muzy/RoboticsResearch/paper/images/mounting.pdf

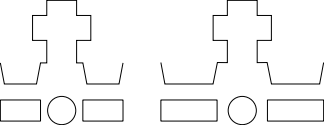
[picture p39: figure]
