muzy/RoboticsResearch/hardware/edubot_board_v01.png

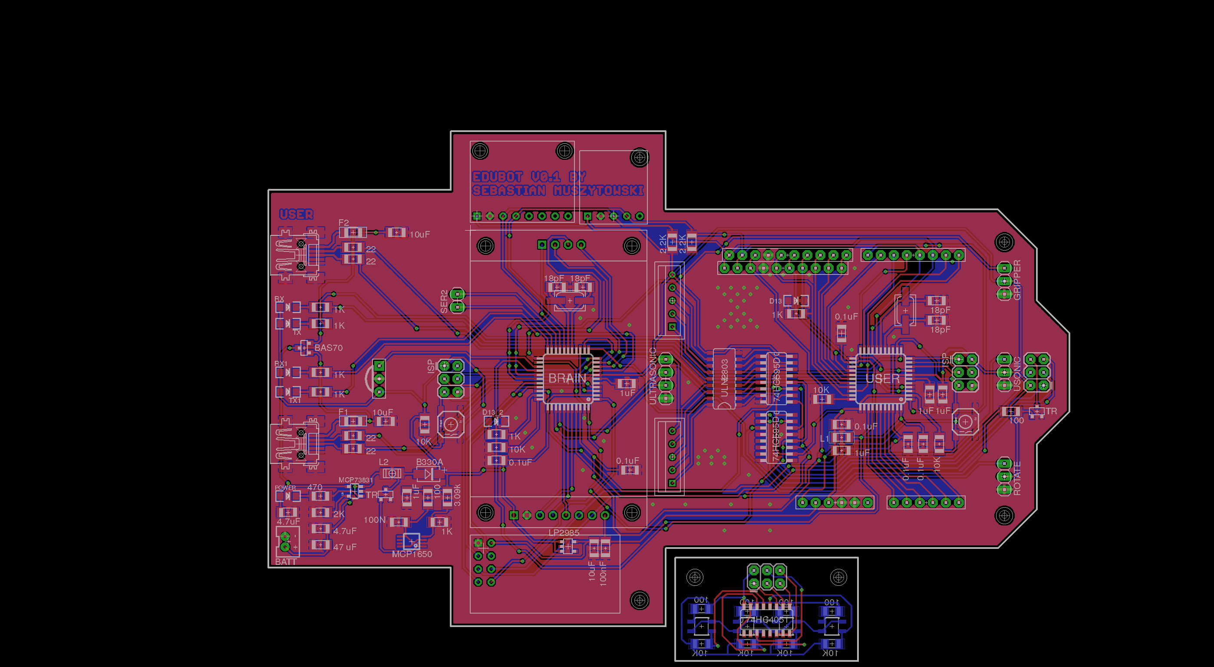
hardware/edubot_board_v01.png
