muzy/RoboticsResearch/hardware/edubot_board_v011.png

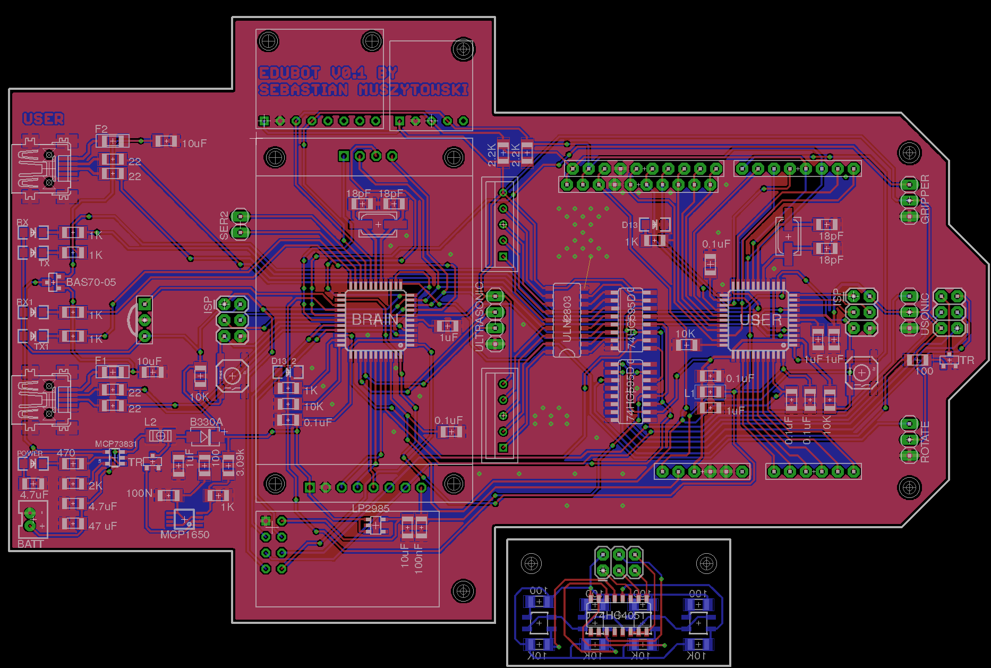
hardware/edubot_board_v011.png
