muzy/RoboticsResearch/hardware/edubot_board_v012.png

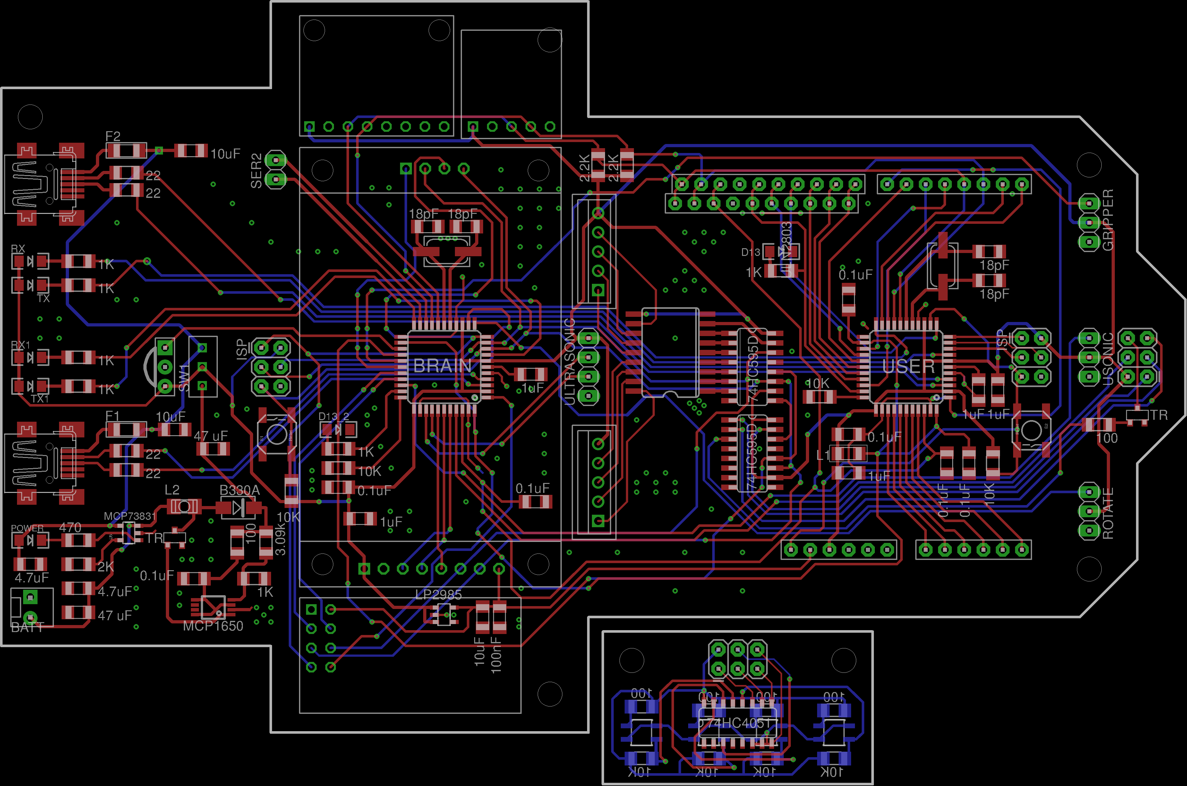
hardware/edubot_board_v012.png
