muzy/RoboticsResearch/hardware/edubot_schematic_v01.png

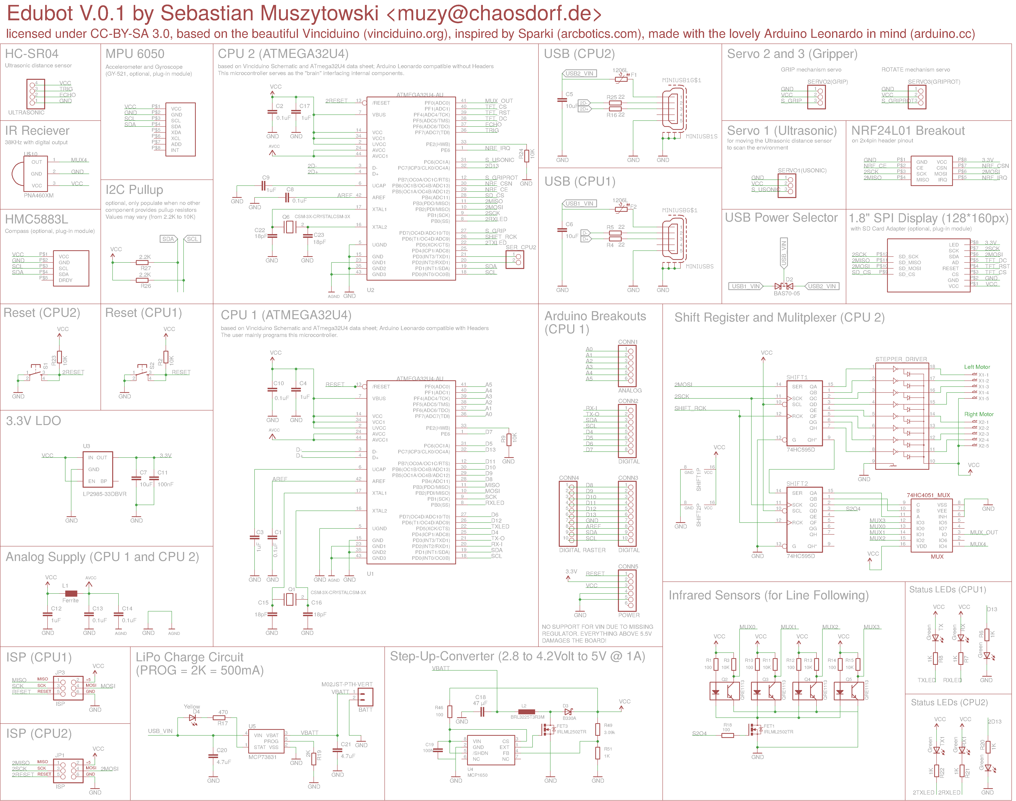
hardware/edubot_schematic_v01.png
