muzy/RoboticsResearch/hardware/edubot_schematic_v012.png

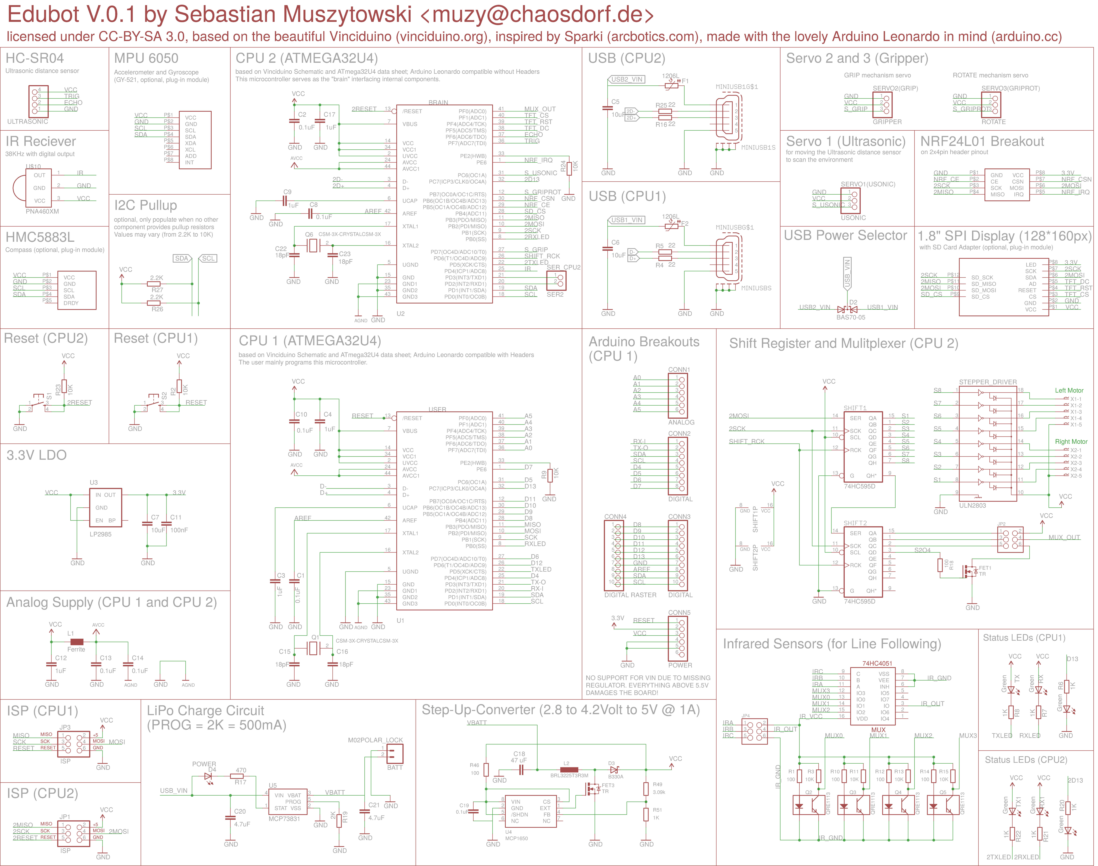
hardware/edubot_schematic_v012.png
