muzy/RoboticsResearch/hardware/schematic_backup_save.png

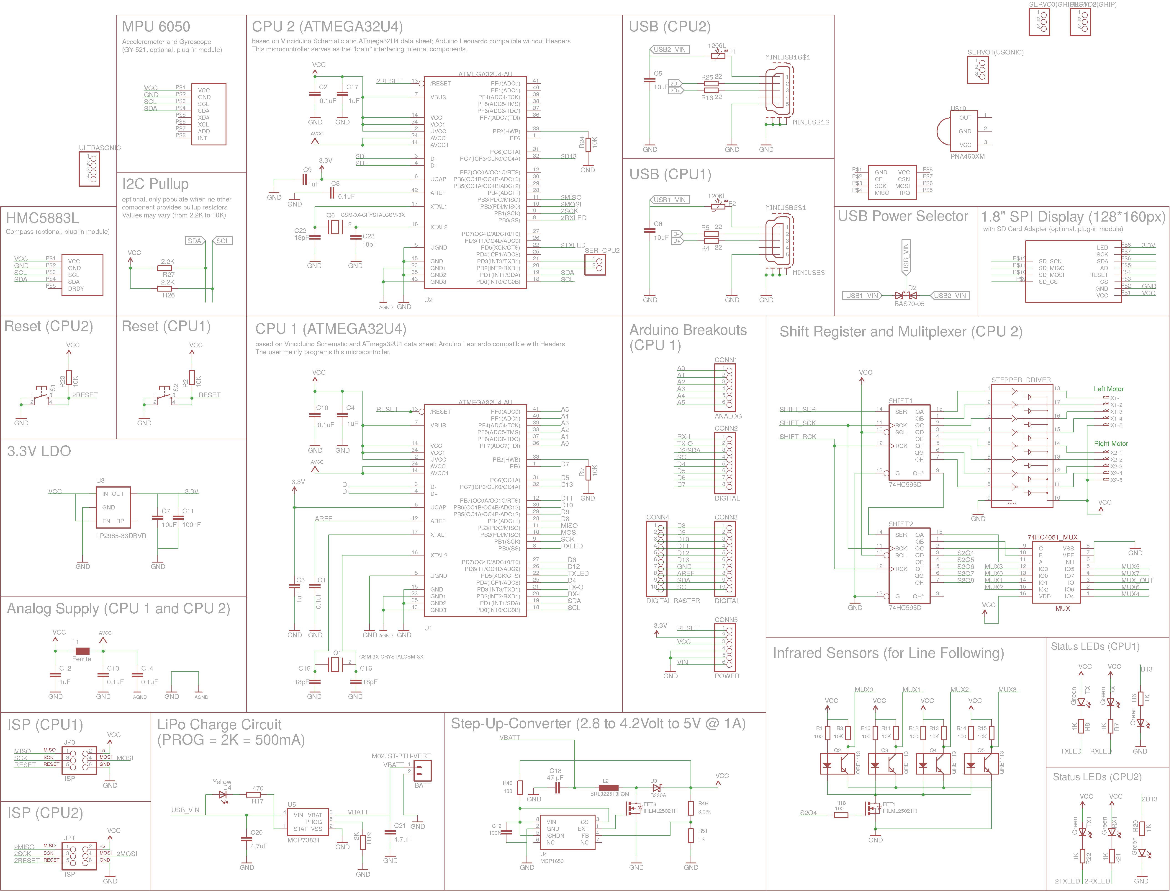
hardware/schematic_backup_save.png
