muzy/RoboticsResearch/paper/images/30_wheel_side.jpg

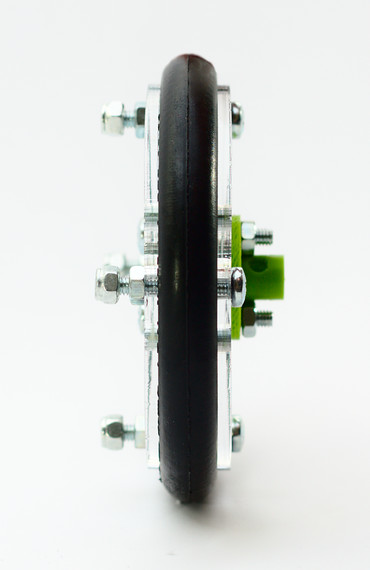
paper/images/30_wheel_side.jpg
