muzy/RoboticsResearch/paper/images/schematic/cpu1.png

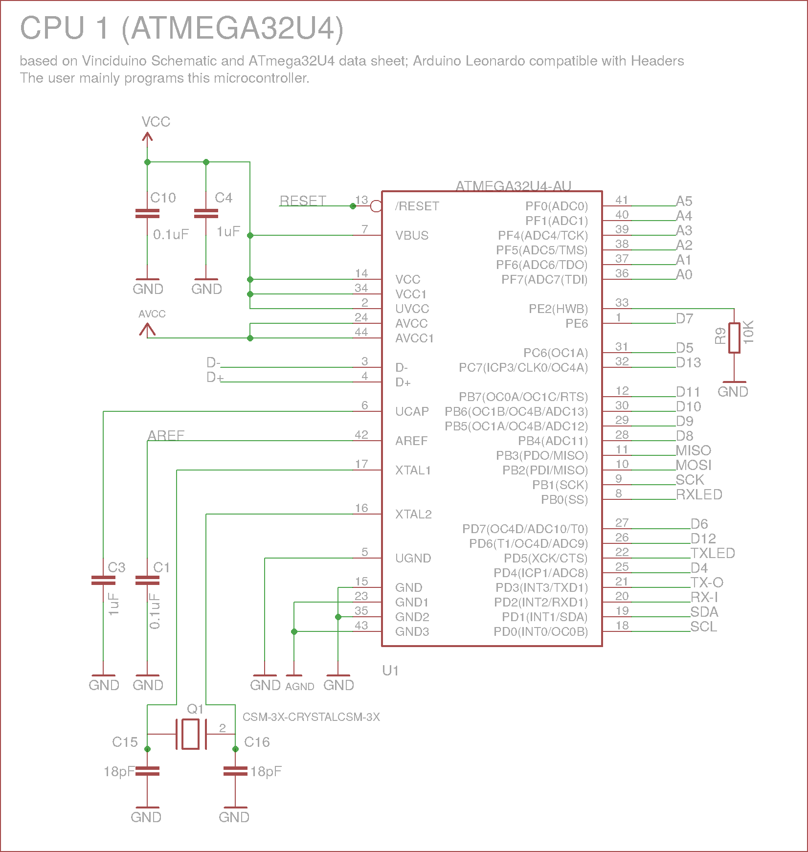
paper/images/schematic/cpu1.png
