muzy/RoboticsResearch/paper/images/schematic/cpu2.png

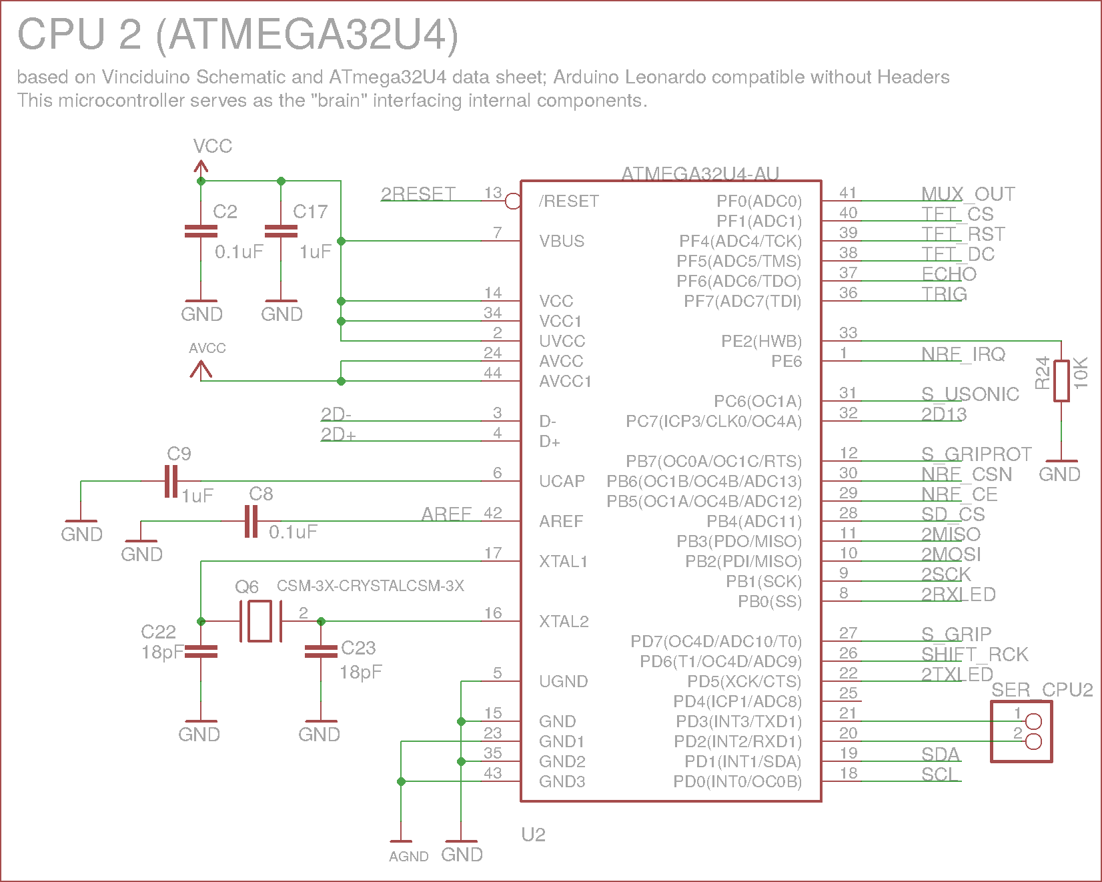
paper/images/schematic/cpu2.png
