muzy/RoboticsResearch/paper/images/schematic/reset.png

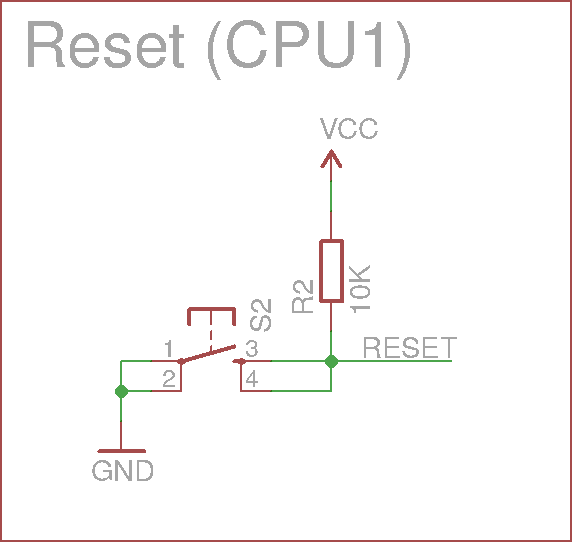
paper/images/schematic/reset.png
