muzy/RoboticsResearch/paper/images/schematic/robot_schematic_optional.png

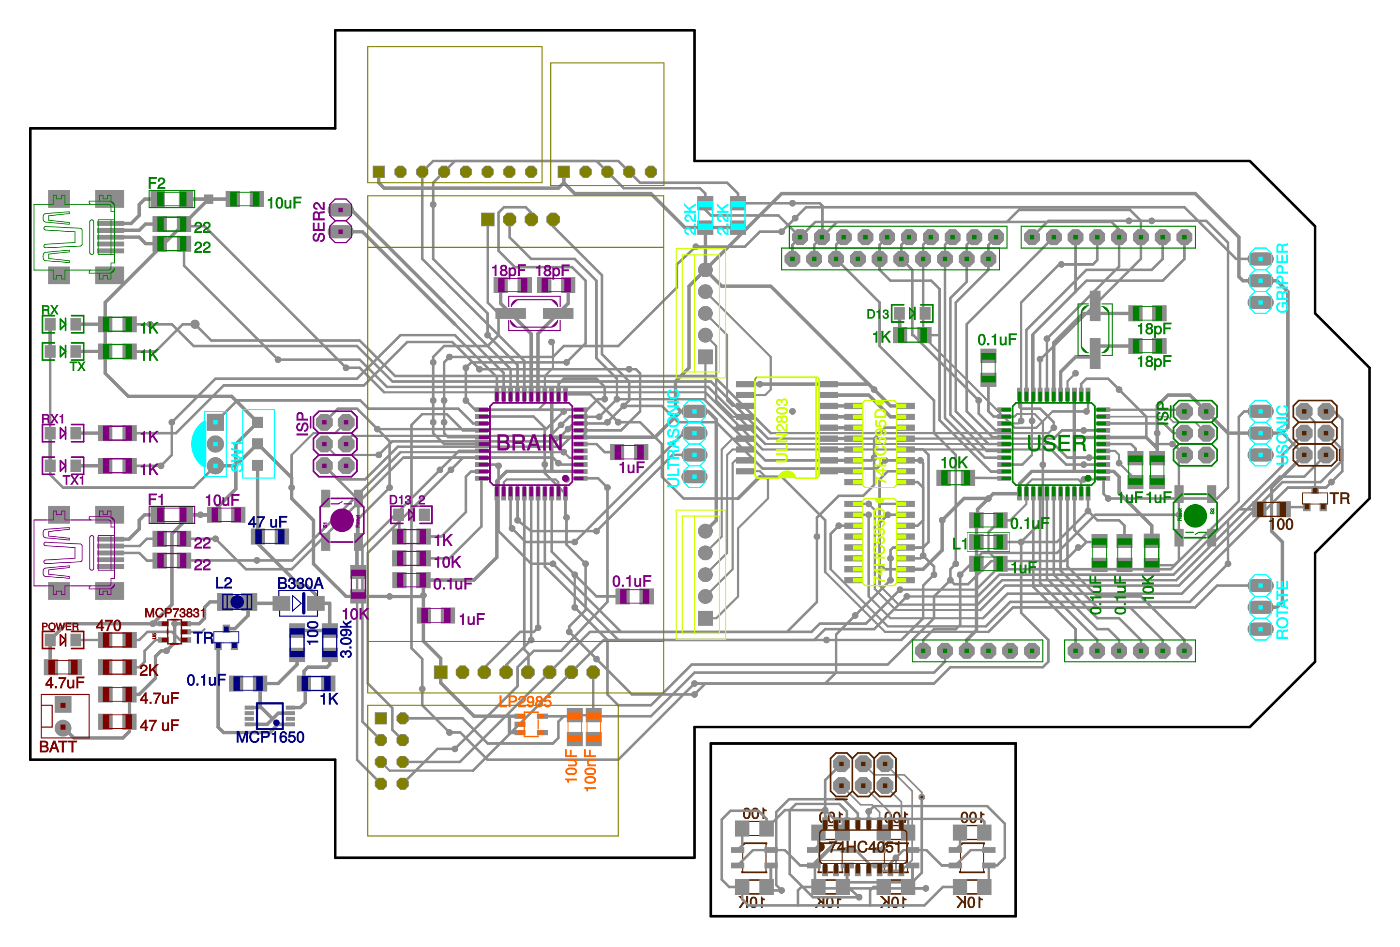
paper/images/schematic/robot_schematic_optional.png
