muzy/RoboticsResearch/paper/images/schematic/shift.png

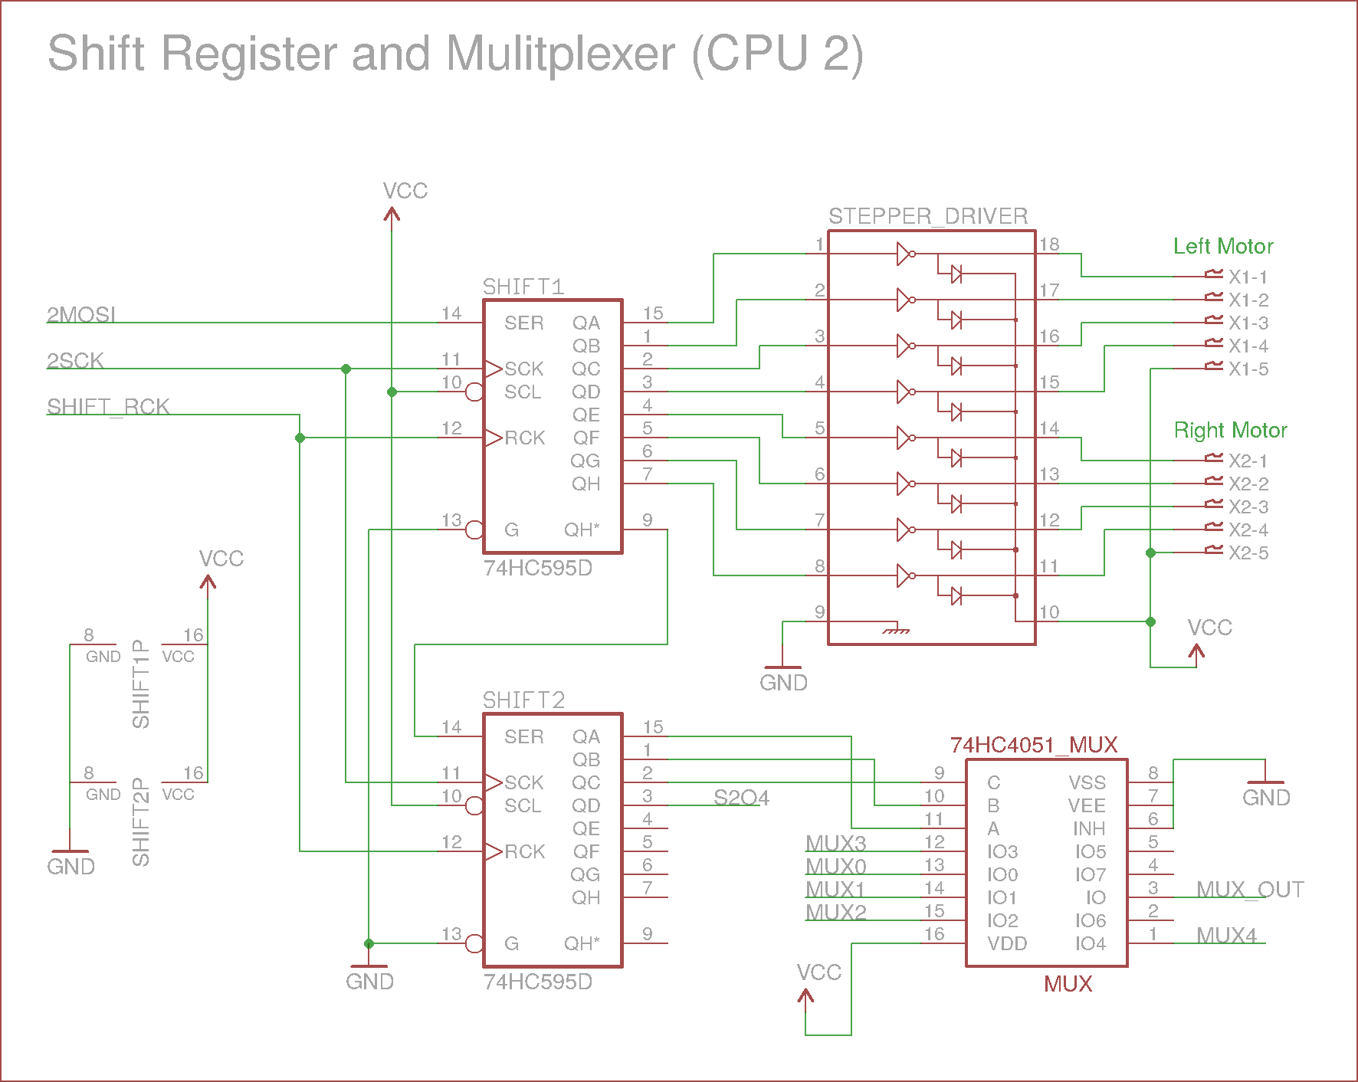
paper/images/schematic/shift.png
