muzy/RoboticsResearch/paper/images/schematic/robot_schematic.pdf

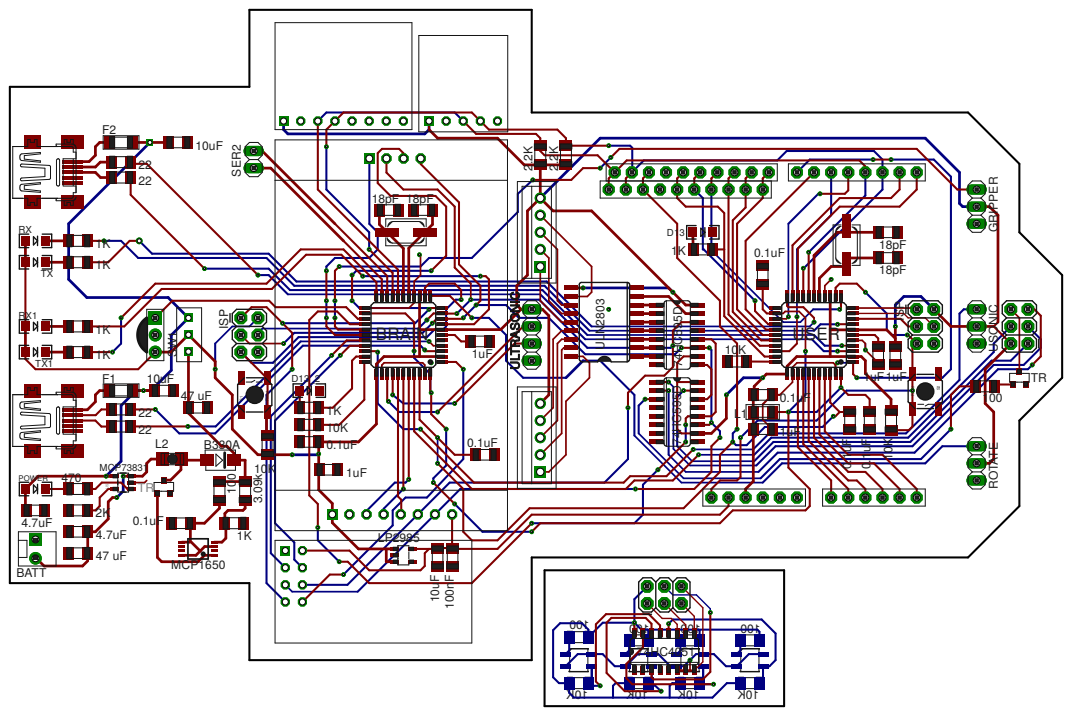
[picture p60: page 1]
BATT; NIC; Reset; ISP; USER; ULN2803; MCP1650; POWER; MCP73831; 10KReset; BRAIN; SER2

USONIC GRIPPER ROTATE
