muzy/RoboticsResearch/paper/images/schematic/robot_schematic_user.pdf

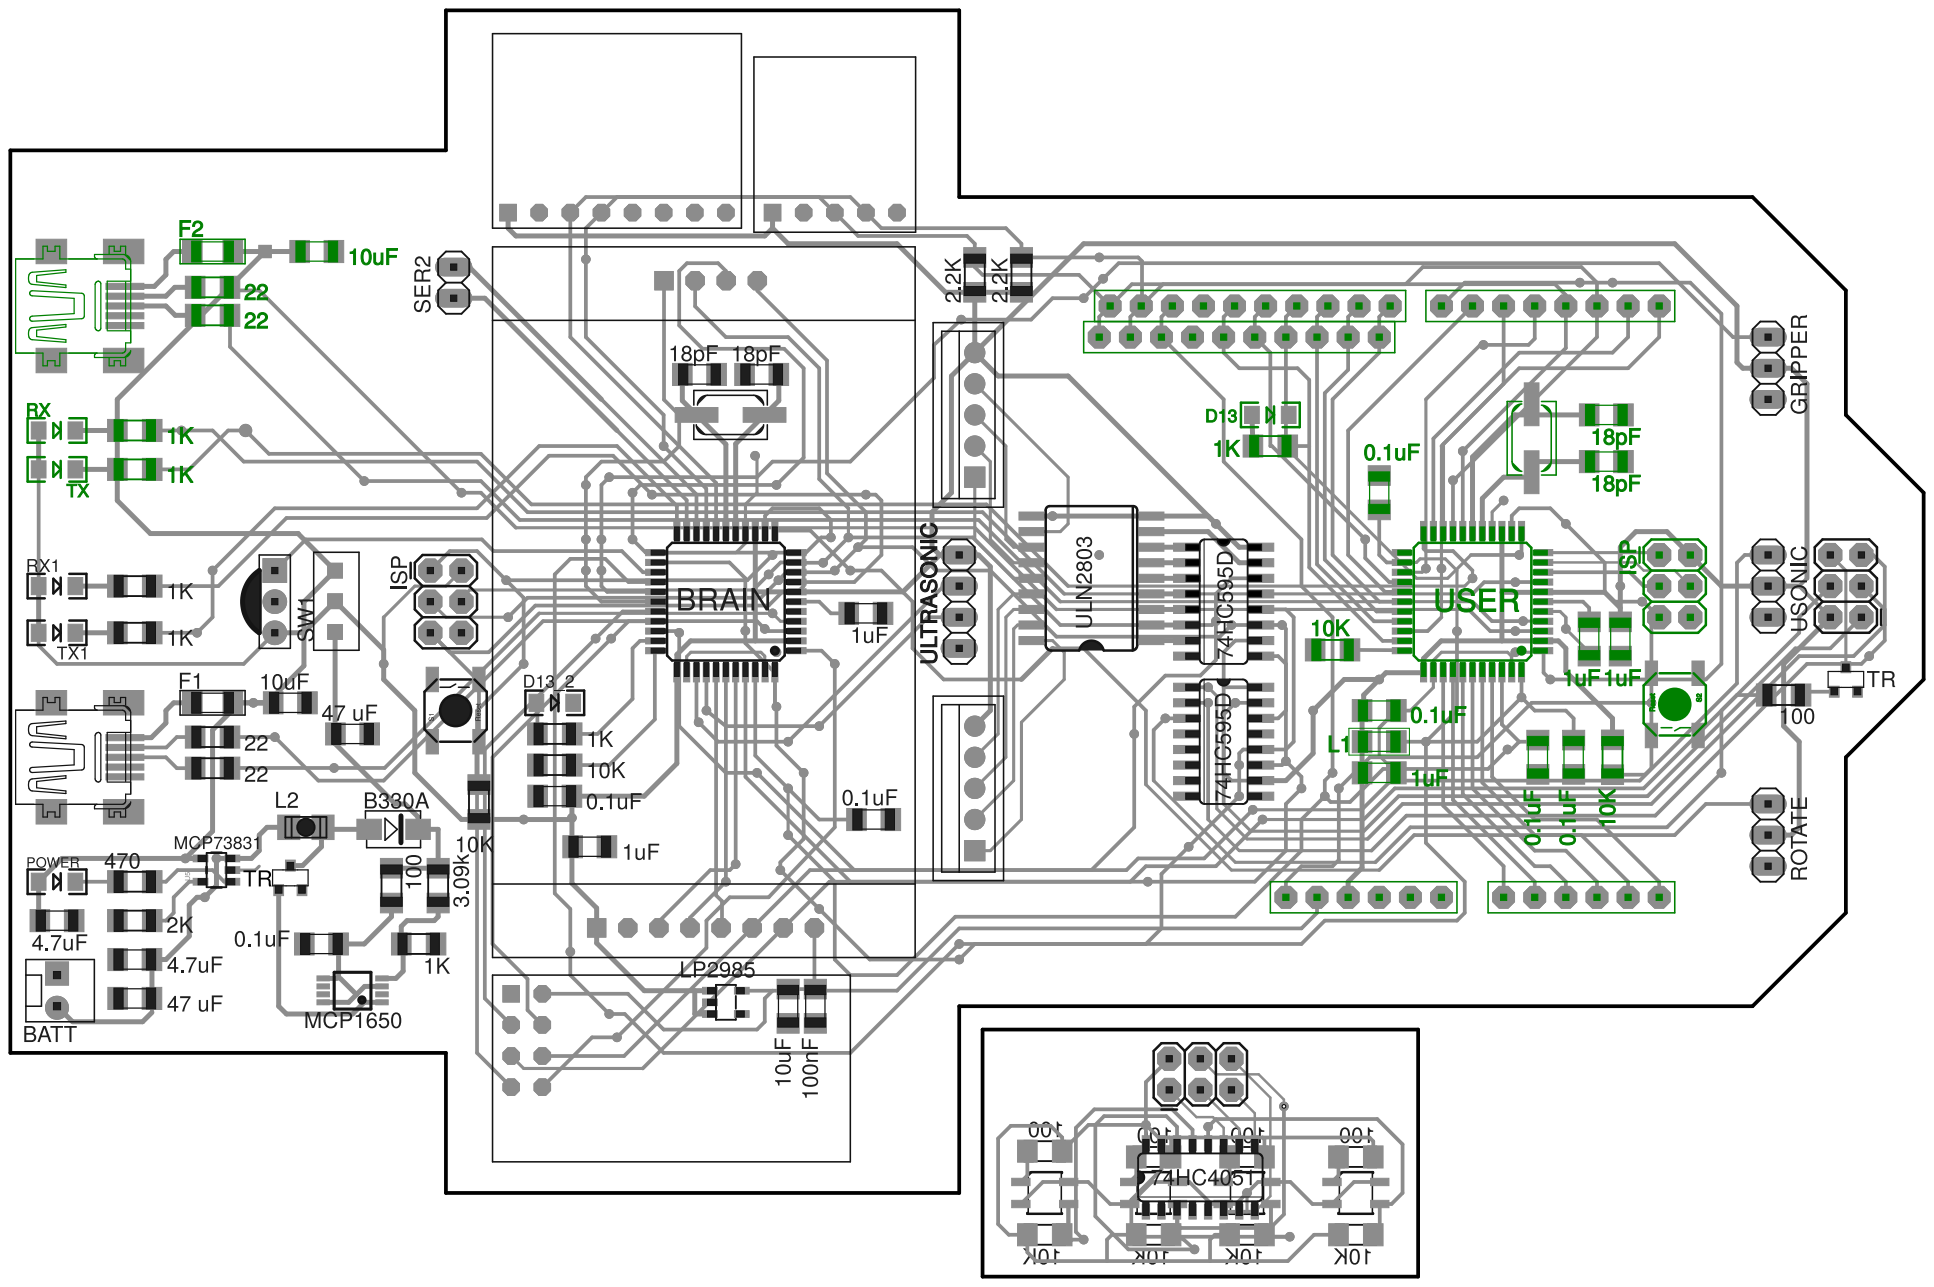
[picture p70: page 1]
